JHorwitz1011/thegoodwand/services/lights/assets/test.csv

250 | #FFFFFF | #000000 | #000000 | #000000 | #000000 | #000000 | #000000 | #000000 | #000000 | #000000 | #000000 | #000000 | #000000 | #000000 | #000000 | #000000 | #000000 | #000000 | #000000 | #000000
250 | #000000 | #FFFFFF | #000000 | #000000 | #000000 | #000000 | #000000 | #000000 | #000000 | #000000 | #000000 | #000000 | #000000 | #000000 | #000000 | #000000 | #000000 | #000000 | #000000 | #000000
250 | #000000 | #000000 | #FFFFFF | #000000 | #000000 | #000000 | #000000 | #000000 | #000000 | #000000 | #000000 | #000000 | #000000 | #000000 | #000000 | #000000 | #000000 | #000000 | #000000 | #000000
250 | #000000 | #000000 | #000000 | #FFFFFF | #000000 | #000000 | #000000 | #000000 | #000000 | #000000 | #000000 | #000000 | #000000 | #000000 | #000000 | #000000 | #000000 | #000000 | #000000 | #000000
250 | #000000 | #000000 | #000000 | #000000 | #FFFFFF | #000000 | #000000 | #000000 | #000000 | #000000 | #000000 | #000000 | #000000 | #000000 | #000000 | #000000 | #000000 | #000000 | #000000 | #000000
250 | #000000 | #000000 | #000000 | #000000 | #000000 | #FFFFFF | #000000 | #000000 | #000000 | #000000 | #000000 | #000000 | #000000 | #000000 | #000000 | #000000 | #000000 | #000000 | #000000 | #000000
250 | #000000 | #000000 | #000000 | #000000 | #000000 | #000000 | #FFFFFF | #000000 | #000000 | #000000 | #000000 | #000000 | #000000 | #000000 | #000000 | #000000 | #000000 | #000000 | #000000 | #000000
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
250 | #000000 | #000000 | #000000 | #000000 | #000000 | #000000 | #000000 | #000000 | #000000 | #000000 | #000000 | #000000 | #000000 | #000000 | #000000 | #000000 | #000000 | #000000 | #000000 | #FFFFFF
