JHorwitz1011/thegoodwand/services/uvlight/pub_client.py

#! /usr/bin/env python3
import time
import json
from paho.mqtt import client as mqtt_client
import sys

broker = 'localhost'
port = 1883
topic = "goodwand/ui/view/uv"
# generate client ID with pub prefix randomly
client_id = f'temp-test-client'

pkt = {
    "header": {
        "type": "UI_LIGHTBAR",
        "version": 1,
    },
    "data": {
        "state": "on",
        "brightness":100,
    }
    }

def connect_mqtt():
    def on_connect(client, userdata, flags, rc):
        if rc == 0:
            print("Connected to MQTT Broker!")
        else:
            print("Failed to connect, return code %d\n", rc)

    client = mqtt_client.Client(client_id)
    client.on_connect = on_connect
    client.connect(broker, port)
    return client


def publish(client):
    msg_count = 0
    time.sleep(1)
    try:
        result = client.publish(topic, json.dumps(pkt))
        # result: [0, 1]
        status = result[0]
        if status == 0:
            print(f"Send {pkt} to topic `{topic}`")
        else:
            print(f"Failed to send message to topic {topic}")
        msg_count += 1
    except IndexError:
        print("ERROR: no argument given. please use format: python3 pub_client.py [animation code]")
    


def run():
    client = connect_mqtt()
    client.loop_start()
    publish(client)




if __name__ == '__main__':
    run()
